pink0D/MiniRaceLogic/LedPatterns_PROGMEM.h

const LedColor led_color_palette[] = {
  {'R',0xFF0000},
  {'G',0x00FF00},
  {'B',0x0000FF},
  {'Y',0xF7B500},
  {'O',0xFF8000},
  {'W',0xAAAAAA}
};
const size_t led_color_palette_size = sizeof(led_color_palette);


const LedPattern led_empty_pattern = {
0,
{
"        ", 
"        ", 
"        ", 
"        "
}
};


const LedPattern led_welcome[] PROGMEM = {
  {
    100,
    {
    "RRRRRRRR", 
    "        ", 
    "        ", 
    "        "
    }
  },
  {
    100,
    {
    "        ", 
    "RRRRRRRR", 
    "        ", 
    "        "
    }
  },
  {
    100,
    {
    "        ", 
    "        ", 
    "RRRRRRRR", 
    "        "
    }
  },
  {
    100,
    {
    "        ", 
    "        ", 
    "        ", 
    "RRRRRRRR"
    }
  },
  {
    100,
    {
    "YYYYYYYY", 
    "        ", 
    "        ", 
    "        "
    }
  },
  {
    100,
    {
    "        ", 
    "YYYYYYYY", 
    "        ", 
    "        "
    }
  },
  {
    100,
    {
    "        ", 
    "        ", 
    "YYYYYYYY", 
    "        "
    }
  },
  {
    100,
    {
    "        ", 
    "        ", 
    "        ", 
    "YYYYYYYY"
    }
  },
  {
    100,
    {
    "GGGGGGGG", 
    "        ", 
    "        ", 
    "        "
    }
  },
  {
    100,
    {
    "        ", 
    "GGGGGGGG", 
    "        ", 
    "        "
    }
  },
  {
    100,
    {
    "        ", 
    "        ", 
    "GGGGGGGG", 
    "        "
    }
  },
  {
    100,
    {
    "        ", 
    "        ", 
    "        ", 
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
    "BBBBBOBB", 
    "        "
    }
  },
  {
    100,
    {
    "        ", 
    "        ", 
    "BBBBBBOB", 
    "        "
    }
  },
  {
    100,
    {
    "        ", 
    "        ", 
    "BBBBBBBO", 
    "        "
    }
  }
};
const size_t led_track_mode_size = sizeof(led_track_mode);
