pink0D/MiniRaceLogic/SoundTones.h

#ifndef _SOUNDTONES_H_
#define _SOUNDTONES_H_

extern const Tone tone_power_on[] PROGMEM;
extern const size_t tone_power_on_size;

extern const Tone tone_power_off[] PROGMEM;
extern const size_t tone_power_off_size;

extern const Tone tone_finish[] PROGMEM;
extern const size_t tone_finish_size;

extern const Tone tone_passthrough[] PROGMEM;
extern const size_t tone_passthrough_size;

extern const Tone tone_false_start[] PROGMEM;
extern const size_t tone_false_start_size;

extern const Tone tone_f1_start[] PROGMEM;
extern const size_t tone_f1_start_size;

extern const Tone tone_simple_start[] PROGMEM;
extern const size_t tone_simple_start_size;

extern const Tone tone_error[] PROGMEM;
extern const size_t tone_error_size;

#endif
